elenamarie25/blueye_autonomy_project/images/Sonar mount.png

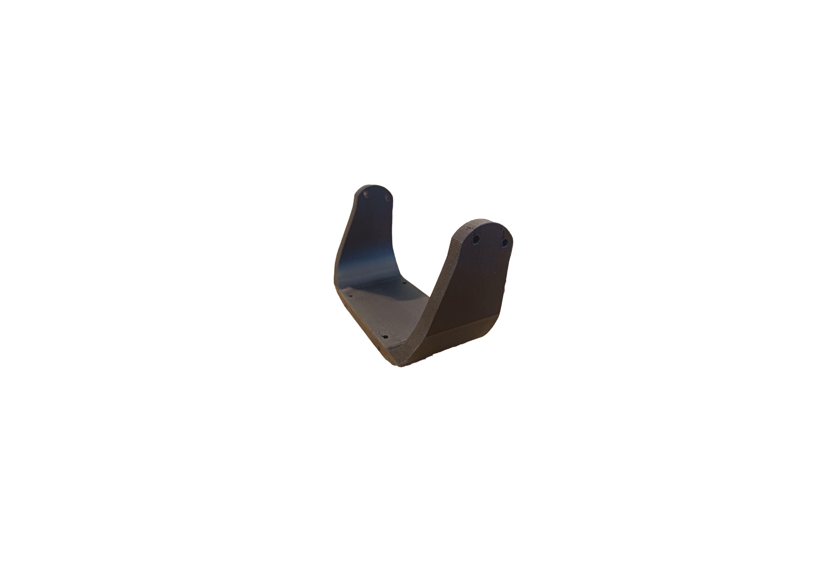
images/Sonar mount.png
