elenamarie25/blueye_autonomy_project/original_files/sensor_mounts/sonar mount.step

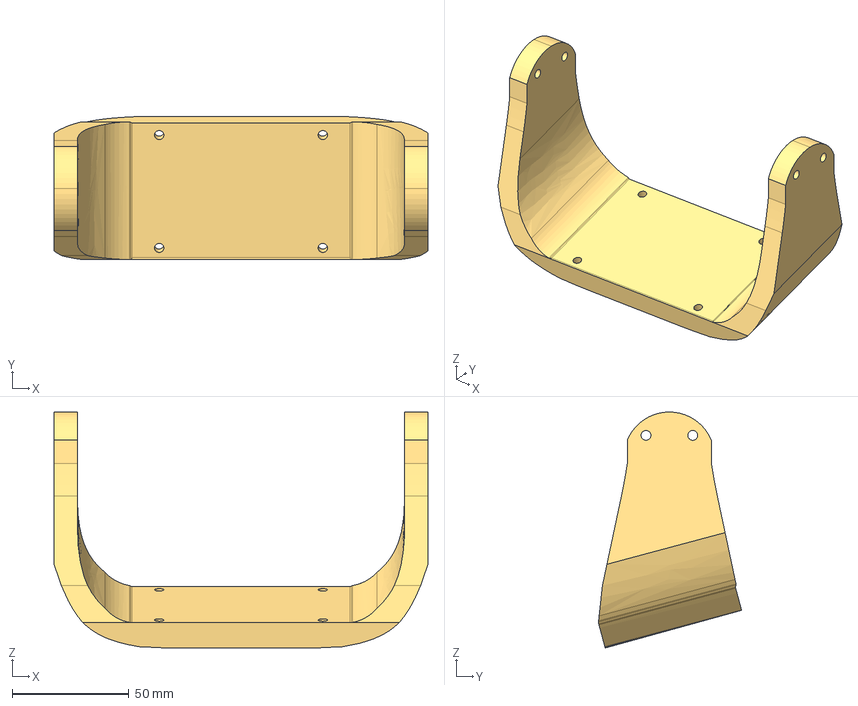
[picture p20: CAD file, 2025-05-12]
original_files/sensor_mounts/sonar mount.step
160.0 x 61.3 x 101.0 mm
