elenamarie25/blueye_autonomy_project/original_files/sensor_mounts/Compute bottle mount.step

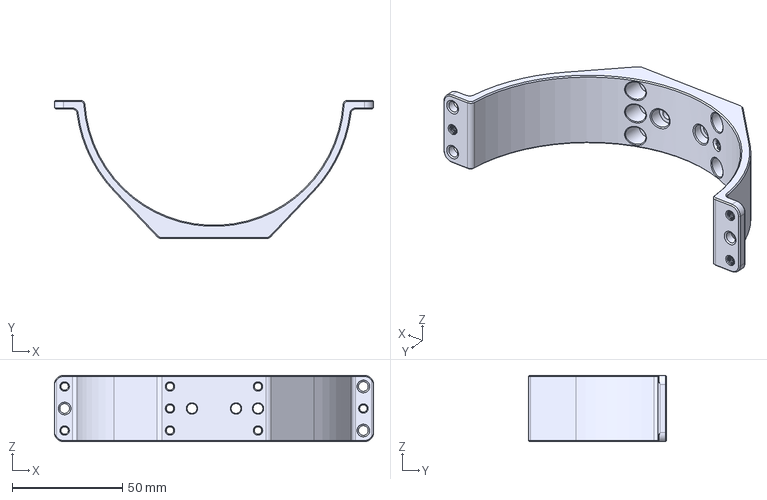
[picture p21: CAD file, 2025-05-06]
original_files/sensor_mounts/Compute bottle mount.step
144.9 x 62.8 x 30.0 mm
