elenamarie25/blueye_autonomy_project/original_files/sensor_mounts/DVL P001 dovetail base mount.step

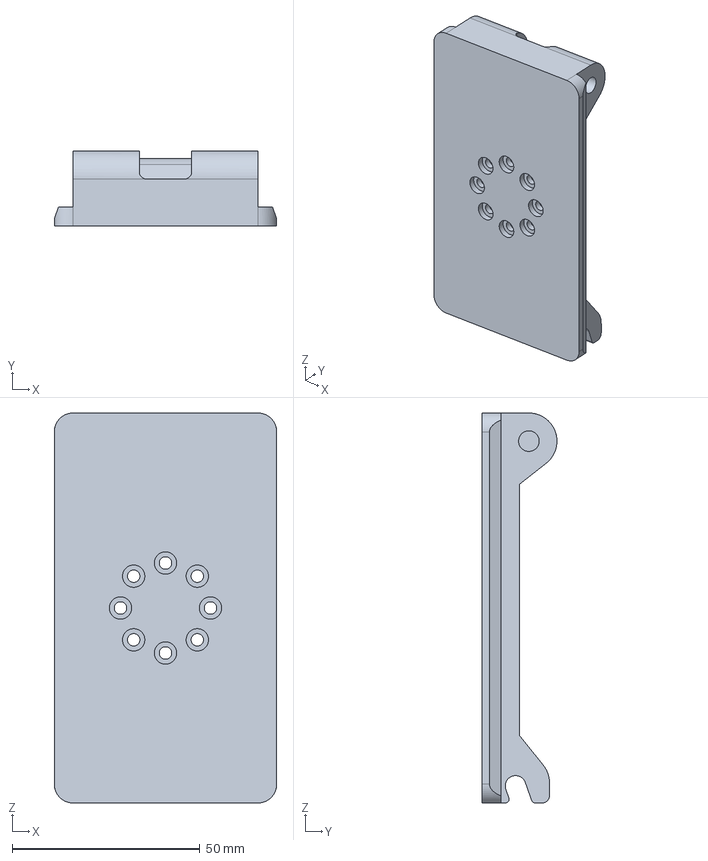
[picture p22: CAD file, 2025-05-06]
original_files/sensor_mounts/DVL P001 dovetail base mount.step
59.3 x 20.0 x 104.0 mm
